TimeEngineer/GreenHouse-Sensor/doc/PCB/alim.PNG

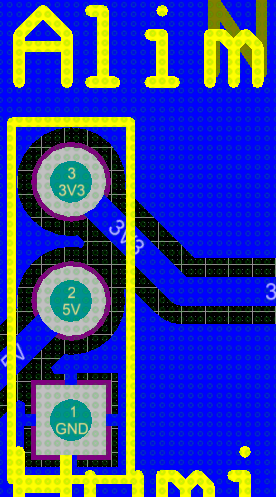
doc/PCB/alim.PNG
