TimeEngineer/GreenHouse-Sensor/doc/PCB/temperature.PNG

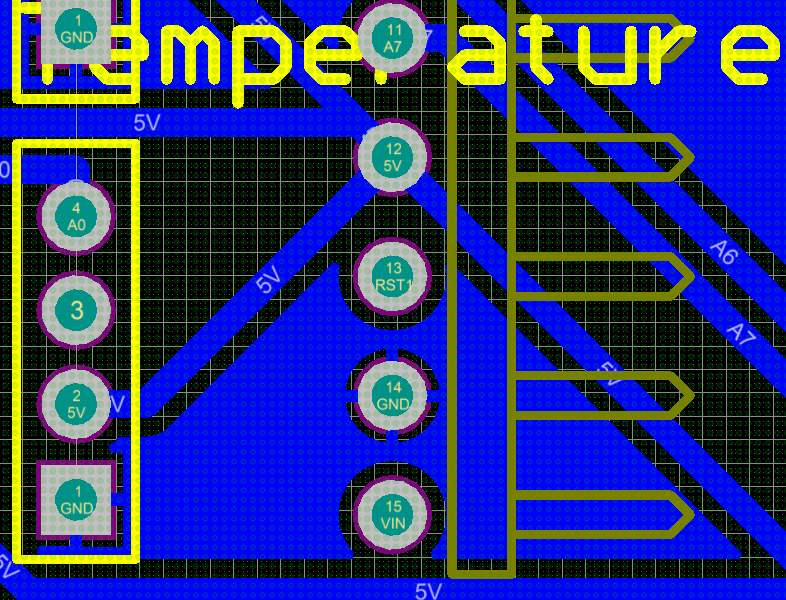
doc/PCB/temperature.PNG
