TimeEngineer/GreenHouse-Sensor/doc/PCB/wisol.PNG

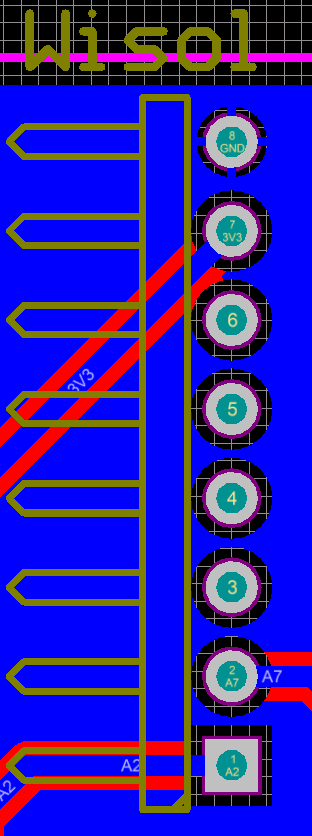
doc/PCB/wisol.PNG
